dirkjankrijnders/decint/3016_21mtc/Outputs/Rev_0/3016-MTC21-3DPreview.png

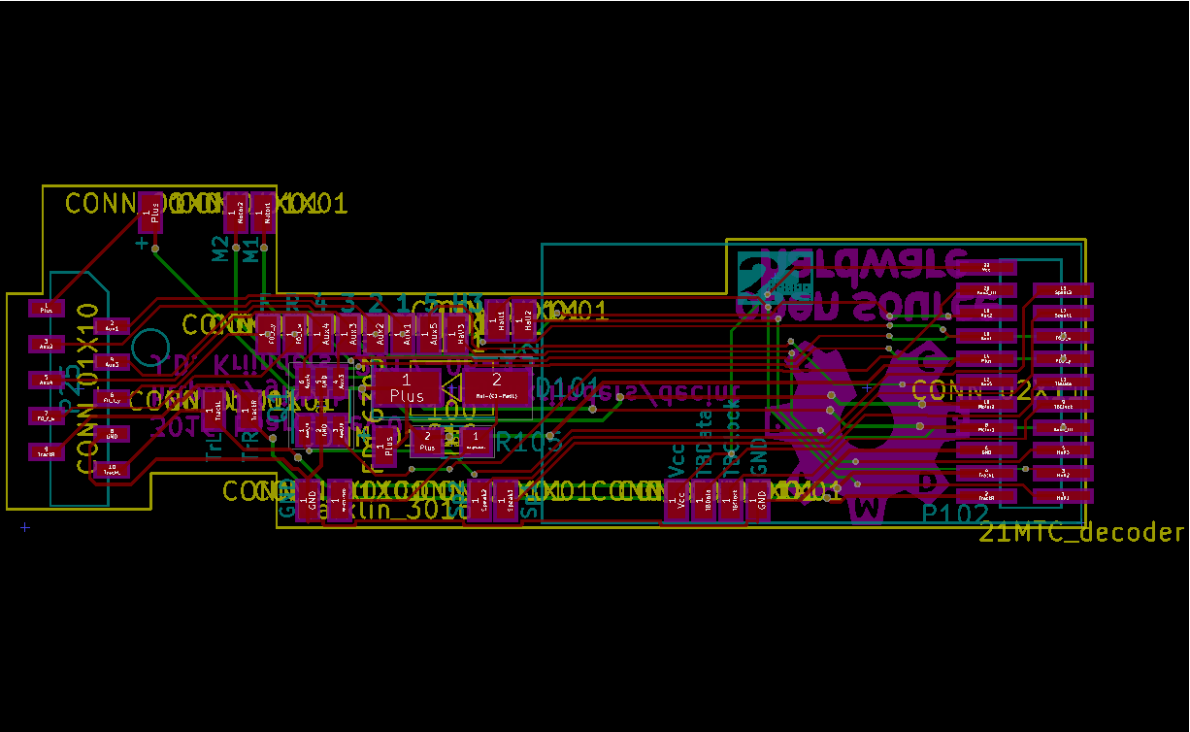
3016_21mtc/Outputs/Rev_0/3016-MTC21-3DPreview.png
